vklachkov/grid-compass-fdd-2102/pal (300230-00)/16L8.jpg

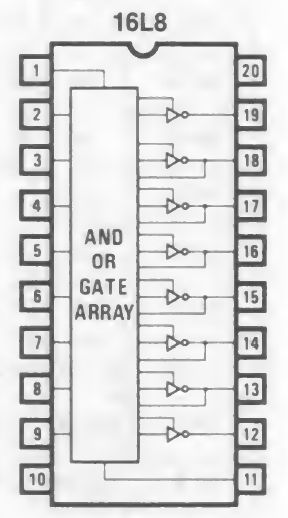
pal (300230-00)/16L8.jpg
