vklachkov/grid-compass-fdd-2102/pal (300230-00)/Logisim_Evolution/PAL16L8.png

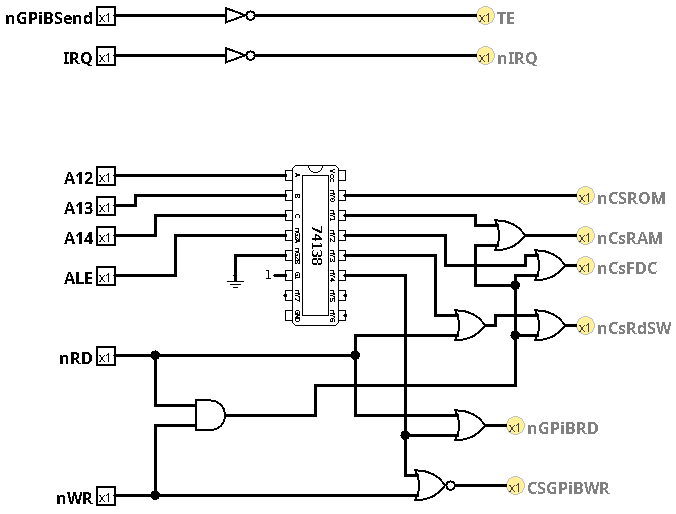
pal (300230-00)/Logisim_Evolution/PAL16L8.png
