vklachkov/grid-compass-fdd-2102/schematic/AC_Wiring.kicad_sch

## KiCad design schematic/AC_Wiring.kicad_sch (2025-12-12)

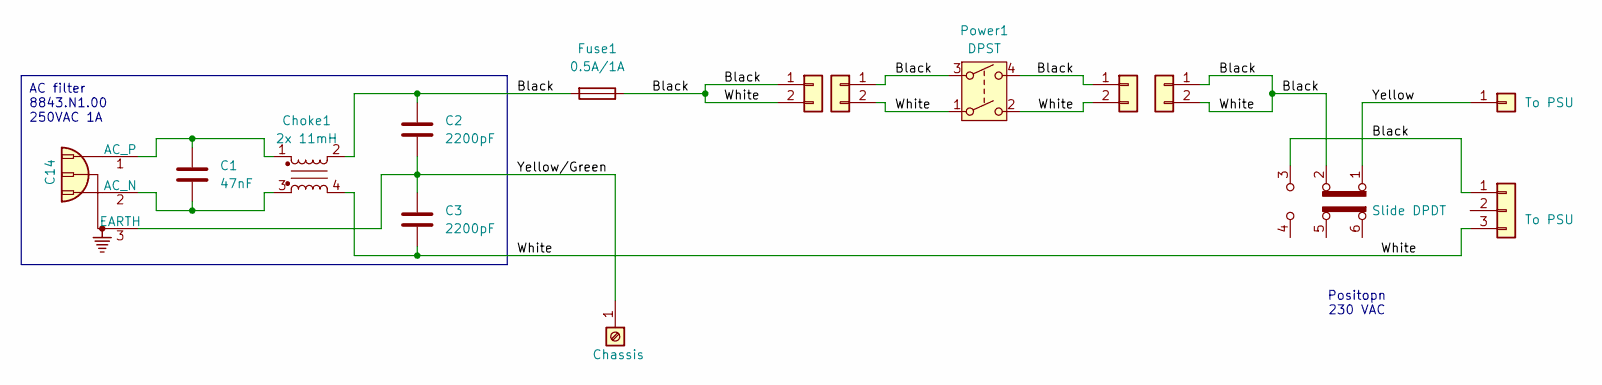
[picture p20: schematic AC_Wiring.kicad_sch]

Parts:
110/1: Slide DPDT
C1: 47nF
C2, C3: 2200pF
Choke1: 2x 11mH; Choke_Schaffner_RN102-04-14.0x14.0mm
Fuse1: 0.5A/1A
J1: C14
J2: Chassis
J3, J4, J5, J6: Conn_01x02
J7: To PSU
J8: To PSU; JST_VH_B3P-VH-B_1x03_P3.96mm_Vertical
Power1: DPST

Connections:
Black: 110/1.2 (B), 110/1.3 (C), C2.1, C3.2, Choke1.2, Choke1.4, Fuse1.1, Fuse1.2, J3.1, J3.2, J4.1, J4.2, J5.1, J5.2, J6.1, J6.2, J8.1, J8.3, Power1.1, Power1.2, Power1.3, Power1.4
unnamed: C1.1, Choke1.1, J1.1 (AC_P)
unnamed: C1.2, Choke1.3, J1.2 (AC_N)
Yellow: 110/1.1 (A), J7.1
Yellow/Green: C2.2, C3.1, J1.3 (EARTH), J2.1

Notes on the sheet:
AC filter 8843.N1.00 250VAC 1A
Positopn 230 VAC
