vklachkov/grid-compass-fdd-2102/schematic/Floppy_Controller_Board.kicad_sch

## KiCad design schematic/Floppy_Controller_Board.kicad_sch (2025-12-12)

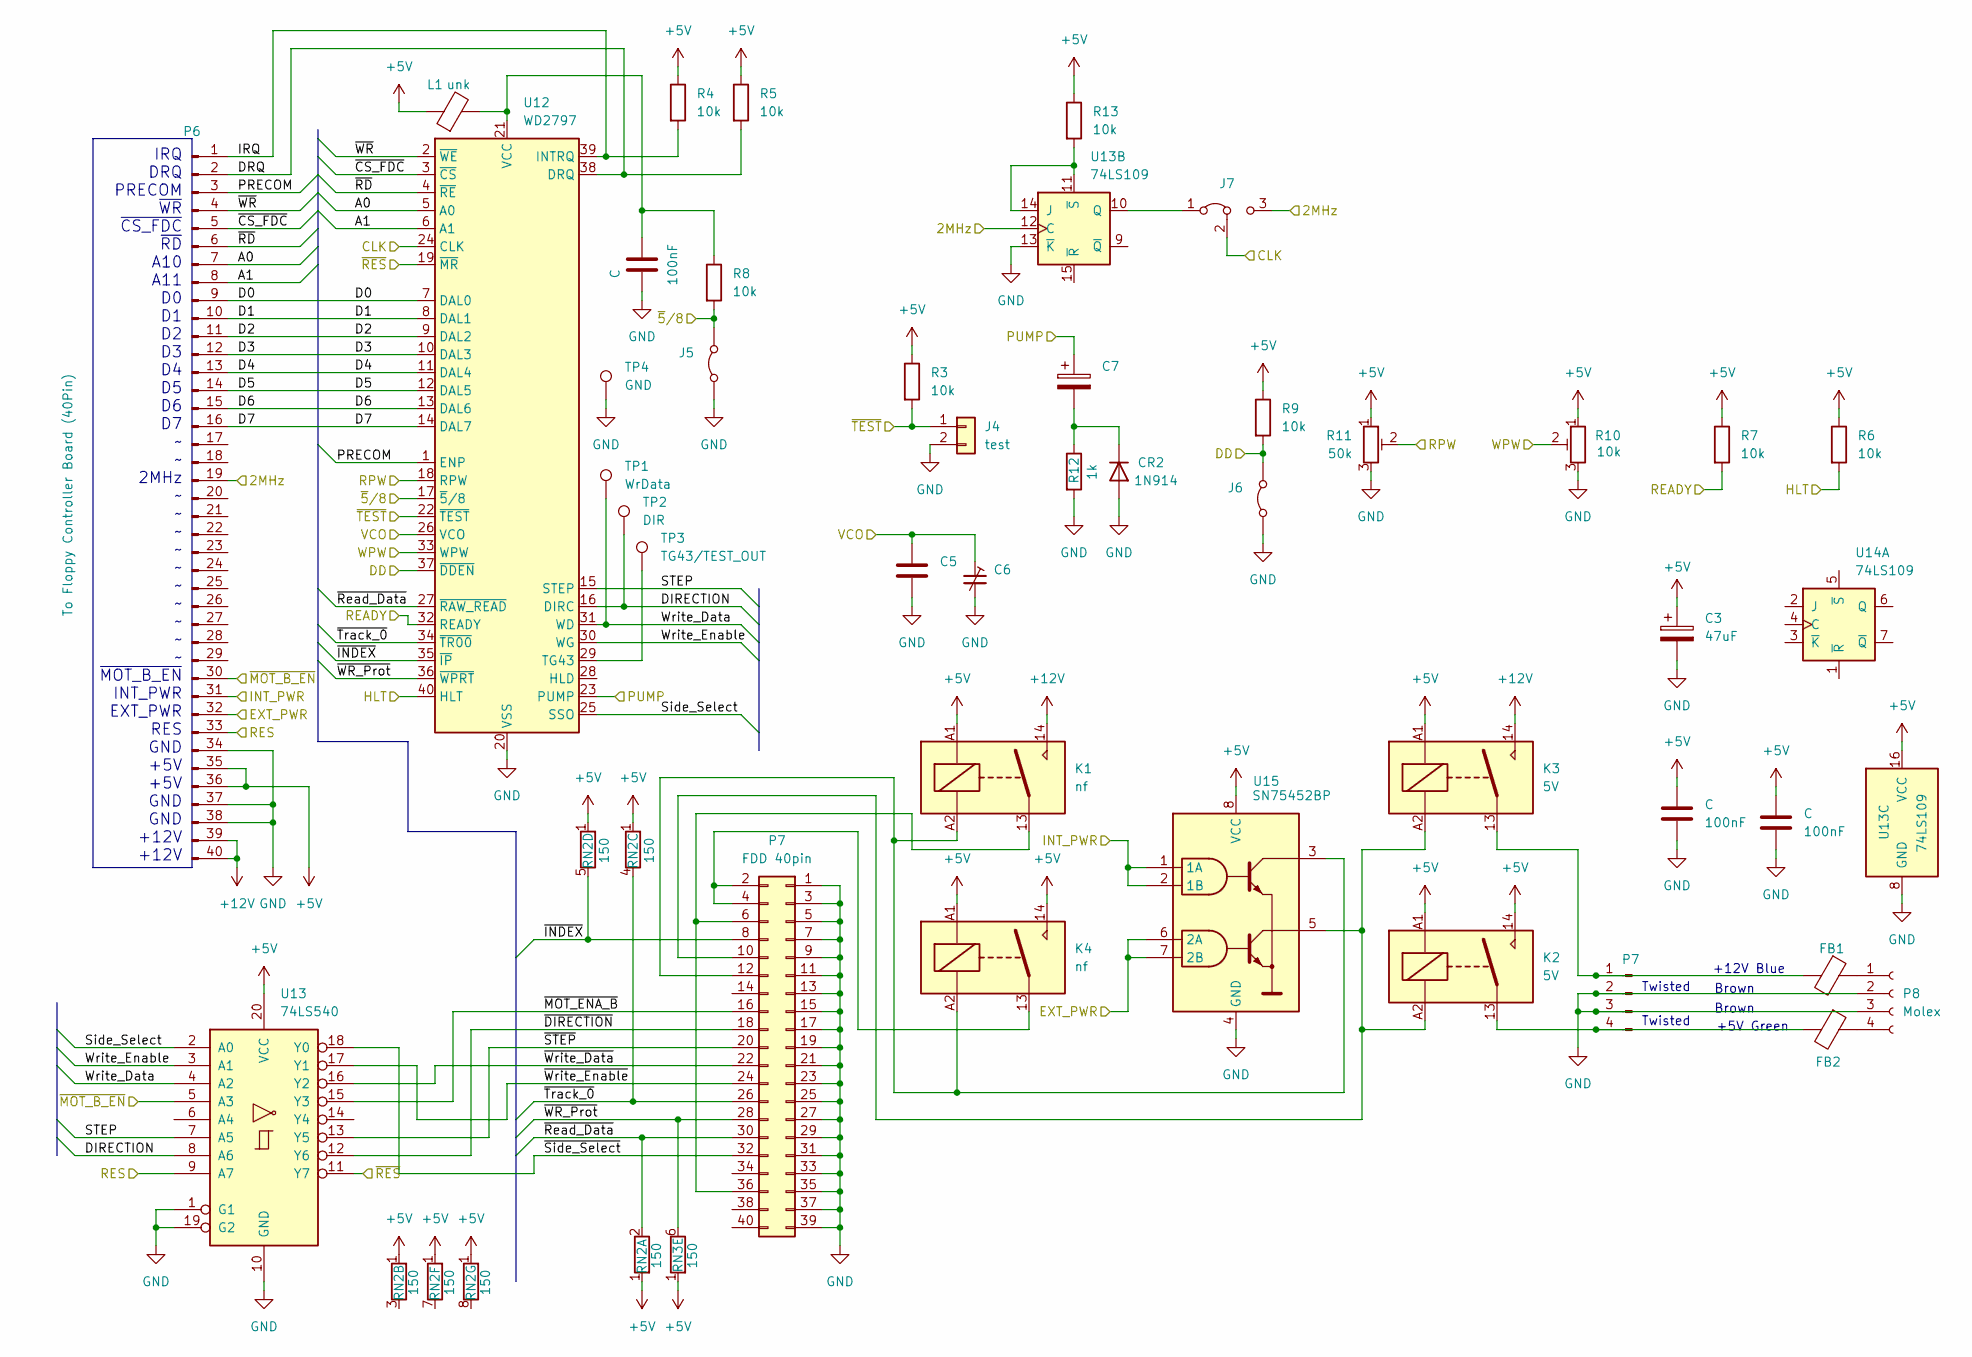
[picture p22: schematic Floppy_Controller_Board.kicad_sch]

Parts:
C: 100nF; C_Disc_D4.3mm_W1.9mm_P5.00mm
C3: 47uF; CP_Axial_L21.0mm_D8.0mm_P28.00mm_Horizontal; Voltage 10V
C5: CP_Axial_L10.0mm_D4.5mm_P15.00mm_Horizontal
C6: C_Disc_D6.0mm_W2.5mm_P5.00mm
C7: CP_Radial_Tantal_D4.5mm_P2.50mm
CR2: 1N914; D_DO-35_SOD27_P10.16mm_Horizontal
FB1, FB2: L_0603_1608Metric
J4: test
J5, J6: (no value)
J7: Jumper_3_Bridged12
K1, K4: nf; Relay_SPST-NO_Fujitsu_FTR-LYAA005x_FormA_Vertical
K2, K3: 5V; Relay_SPST-NO_Fujitsu_FTR-LYAA005x_FormA_Vertical
L1: unk
P6: To Floppy Controller Board (40Pin)
P7: FDD 40pin
P8: Molex; TE_MATE-N-LOK_350211-1_1x04_P5.08mm_Vertical
R3, R4, R5, R6, R7, R8, R9, R13: 10k; R_Axial_DIN0309_L9.0mm_D3.2mm_P12.70mm_Horizontal
R10: 10k; Potentiometer_ACP_CA6-H2,5_Horizontal
R11: 50k; Potentiometer_ACP_CA6-H2,5_Horizontal
R12: 1k; R_Axial_DIN0309_L9.0mm_D3.2mm_P12.70mm_Horizontal
RN2, RN3: 150; R_Array_SIP8
TP1: WrData
TP2: DIR
TP3: TG43/TEST_OUT
TP4: GND
U12: WD2797; DIP-40_W15.24mm
U13, U14: 74LS109; DIP-16_W7.62mm
U15: SN75452BP; DIP-8_W7.62mm

Connections:
2MHz: J7.3 (B), P6.19, U13.12 (Y6)
+5V: C.1, C3.1, K1.A1, K2.14, K2.A1, K3.A1, K4.14, K4.A1, L1.1, P6.35, P6.36, R3.1, R4.1, R5.1, R6.1, R7.1, R9.1, R10.1, R11.1, R13.1, RN2.1 (R1), RN3.1 (R1), U13.16 (Y2), U13.20 (VCC), U15.8 (VCC)
+12V: K1.14, K3.14, P6.39, P6.40
A0: P6.7, U12.5 (A0)
A1: P6.8, U12.6 (A1)
CLK: J7.2 (C), U12.24 (CLK)
D0: P6.9, U12.7 (DAL0)
D1: P6.10, U12.8 (DAL1)
D2: P6.11, U12.9 (DAL2)
D3: P6.12, U12.10 (DAL3)
D4: P6.13, U12.11 (DAL4)
D5: P6.14, U12.12 (DAL5)
D6: P6.15, U12.13 (DAL6)
D7: P6.16, U12.14 (DAL7)
DD: J6.2 (B), R9.2, U12.37 (~DDEN)
DIRECTION: TP2.1, U12.16 (DIRC), U13.8 (A6)
DRQ: P6.2, R5.2, U12.38 (DRQ)
EXT_PWR: P6.32, U15.6 (2A), U15.7 (2B)
GND: C.2, C3.2, C5.2, C6.2, CR2.2 (A), J4.2, J5.1 (A), J6.1 (A), P6.34, P6.37, P6.38, P7.1, P7.2, P7.3, P7.5, P7.7, P7.9, P7.11, P7.13, P7.15, P7.17, P7.19, P7.21, P7.23, P7.25, P7.27, P7.29, P7.31, P7.33, P7.35, P7.37, P7.39, P8.2, P8.3, R10.3, R11.3, R12.2, TP4.1, U12.20 (VSS), U13.1 (G1), U13.8 (A6), U13.10 (GND), U13.13 (Y5), U13.19 (G2), U15.4 (GND)
HLT: R6.2, U12.40 (HLT)
INT_PWR: P6.31, U15.1 (1A), U15.2 (1B)
IRQ: P6.1, R4.2, U12.39 (INTRQ)
unnamed: C7.2, CR2.1 (K), R12.1
unnamed: C.1, L1.2, R8.1, U12.21 (VCC)
unnamed: FB1.1, P8.1
unnamed: FB1.2, K3.13, P7.1
unnamed: FB2.1, P8.4
unnamed: FB2.2, K2.13, P7.4
unnamed: J7.1 (A), U13.10 (GND)
unnamed: K1.13, P7.6, P7.36
unnamed: K1.A2, K4.A2, P7.12, U15.3
unnamed: K2.A2, K3.A2, P7.10, U15.5
unnamed: K4.13, P7.2, P7.4
unnamed: R13.2, U13.11 (Y7), U13.14 (Y4)
unnamed: TP3.1, U12.29 (TG43)
PRECOM: P6.3, U12.1 (ENP)
PUMP: C7.1, U12.23 (PUMP)
READY: R7.2, U12.32 (READY)
RES: P6.33, U13.9 (A7)
RPW: R11.2, U12.18 (RPW)
STEP: U12.15 (STEP), U13.7 (A5)
Side_Select: U12.25 (SSO), U13.2 (A0)
VCO: C5.1, C6.1, U12.26 (VCO)
WPW: R10.2, U12.33 (WPW)
Write_Data: TP1.1, U12.31 (WD), U13.4 (A2)
Write_Enable: U12.30 (WG), U13.3 (A1)
~5/8: J5.2 (B), R8.2, U12.17 (~5/8)
~CS_FDC: P6.5, U12.3 (~CS)
~DIRECTION: P7.18, U13.12 (Y6)
~INDEX: P7.8, RN2.5 (R4.2), U12.35 (~IP)
~MOT_B_EN: P6.30, U13.5 (A3)
~MOT_ENA_B: P7.16, U13.15 (Y3)
~RD: P6.6, U12.4 (~RE)
~RES: U12.19 (~MR), U13.11 (Y7)
~Read_Data: P7.30, RN2.2 (R1.2), U12.27 (~RAW_READ)
~STEP: P7.20, U13.13 (Y5)
~Side_Select: P7.32, U13.18 (Y0)
~TEST: J4.1, R3.2, U12.22 (~TEST)
~Track_0: P7.26, RN2.4 (R3.2), U12.34 (~TR00)
~WR_Prot: P7.28, RN3.6 (R5.2), U12.36 (~WPRT)
~WR: P6.4, U12.2 (~WE)
~Write_Data: P7.22, U13.16 (Y2)
~Write_Enable: P7.24, U13.17 (Y1)

Notes on the sheet:
IRQ DRQ PRECOM ~{WR} ~{CS_FDC} ~{RD} A10 A11 D0 D1 D2 D3 D4 D5 D6 D7 ~ ~ 2MHz ~ ~ ~ ~ ~ ~ ~ ~ ~ ~ ~{MOT_B_EN} INT_PWR EXT_PWR RES GND +5V +5V GND GND +12V +12V
Brown
+12V Blue
+5V Green
Twisted
