vklachkov/grid-compass-fdd-2102/schematic/GPiB_connector.kicad_sch

## KiCad design schematic/GPiB_connector.kicad_sch (2025-12-12)

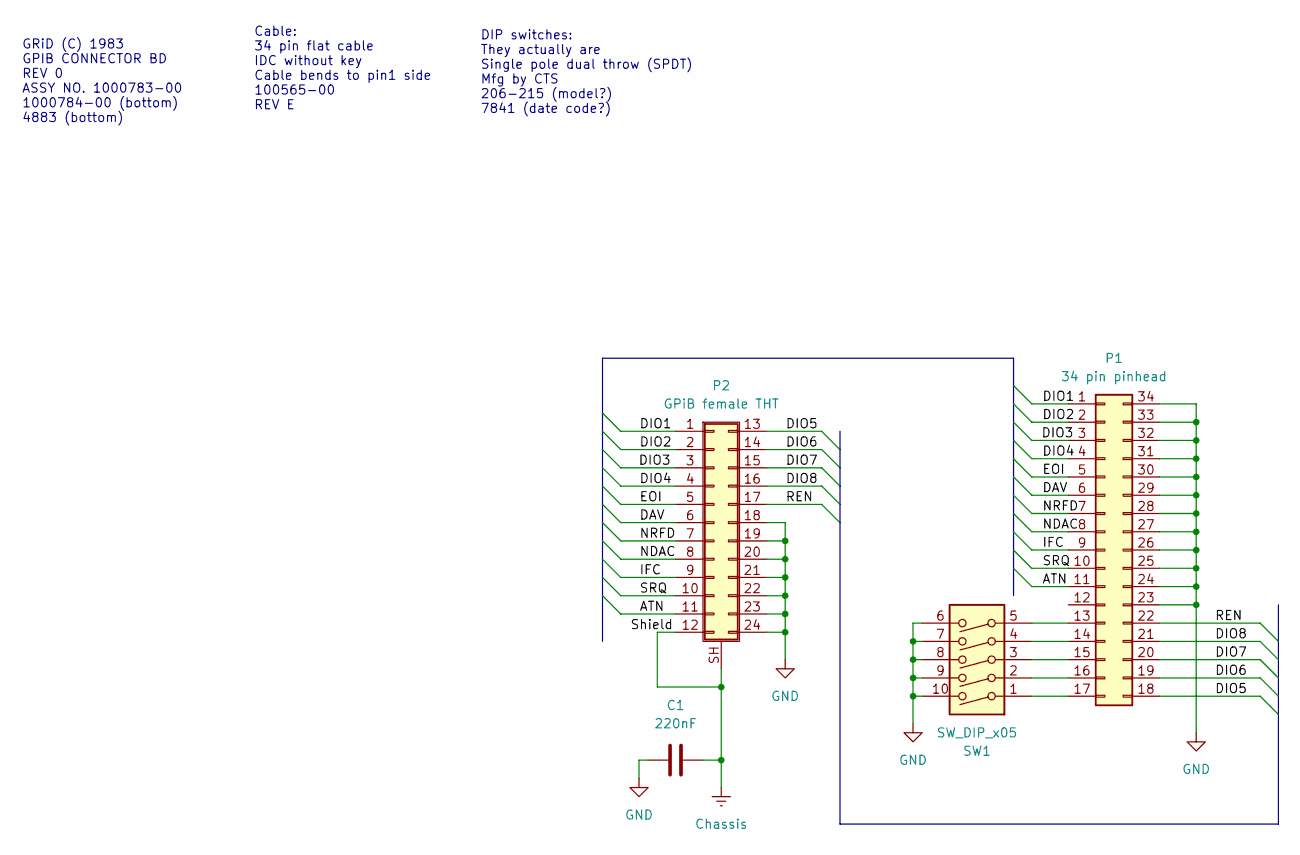
[picture p24: schematic GPiB_connector.kicad_sch]

Parts:
C1: 220nF; C_Rect_L10.0mm_W2.5mm_P7.50mm_MKS4; Voltage 100V
P1: 34 pin pinhead
P2: GPiB female THT
SW1: SW_DIP_x05

Connections:
ATN: P1.11, P2.11
Chassis: C1.2, P2.12, P2.SH (Shield)
DAV: P1.6, P2.6
DIO1: P1.1, P2.1
DIO2: P1.2, P2.2
DIO3: P1.3, P2.3
DIO4: P1.4, P2.4
DIO5: P1.18, P2.13
DIO6: P1.19, P2.14
DIO7: P1.20, P2.15
DIO8: P1.21, P2.16
EOI: P1.5, P2.5
GND: C1.1, P1.23, P1.24, P1.25, P1.26, P1.27, P1.28, P1.29, P1.30, P1.31, P1.32, P1.33, P1.34, P2.18, P2.19, P2.20, P2.21, P2.22, P2.23, P2.24, SW1.6, SW1.7, SW1.8, SW1.9, SW1.10
IFC: P1.9, P2.9
NDAC: P1.8, P2.8
NRFD: P1.7, P2.7
unnamed: P1.13, SW1.5
unnamed: P1.14, SW1.4
unnamed: P1.15, SW1.3
unnamed: P1.16, SW1.2
unnamed: P1.17, SW1.1
REN: P1.22, P2.17
SRQ: P1.10, P2.10

Notes on the sheet:
Cable: 34 pin flat cable IDC without key Cable bends to pin1 side 100565-00 REV E
DIP switches: They actually are Single pole dual throw (SPDT) Mfg by CTS 206-215 (model?) 7841 (date code?)
GRiD (C) 1983 GPIB CONNECTOR BD REV 0 ASSY NO. 1000783-00 1000784-00 (bottom) 4883 (bottom)
