vklachkov/grid-compass-fdd-2102/pal (300230-00)/PAL16L8_dumper/megaprogrammer28.py

#!/usr/bin/env python
# Uses the Arduino firmware given on http://danceswithferrets.org/geekblog/?p=496
#
# -r start end (in decimal) dump address+data+checksum
# -R start end (in decimal) dump only data
# -b start end (in decimal) dump in binary
# -s file.bin (programming)
# -v file.bin (verify content)
# -S file.bin ('smart' programming)
#
# Normally takes 196 seconds to program a 28C64, and 32 seconds to read.
# --
# Chris Baird,, <cjb@brushtail.apana.org.au> threw
# this together during an all-nighter on 2017-Oct-19.
# This version: 2017-Oct-25.

from __future__ import print_function

import sys
import serial
import time
import os

RECSIZE = 16

# ser = serial.Serial('/dev/ttyACM0', 115200, timeout=0.1)
ser = serial.Serial('/dev/ttyUSB0', 115200, timeout=0.1)
# ser = open('serial_out.dbg', 'wb')  # DBG

sys.argv.pop(0)
dumpstart = -1
dumpend = -1
s = sys.argv[0]
time.sleep(1)                   # weirdness it started needing -cjb
ser.flush()
time.sleep(1)

PY3 = sys.version_info[0] >= 3


def ord_compat(c):
    if PY3:
        return c
    else:
        return ord(c)

def bytes_compat(s):
    if PY3:
        return s.encode()
    else:
        return s


def calcwriteline(a, l):
    ck = 0
    s = "W" + ("%05x" % a) + ":"
    for c in l:
        s = s + ("%02x" % ord_compat(c))
        ck = ck ^ ord_compat(c)
    s = s + "ffffffffffffffffffffffffffffffff"
    #print(s)
    s = s[:39]
    if (len(l) & 1):
        ck = ck ^ 255
    ck = ck & 255
    s = s + "," + ("%02x" % ck)
    return s.upper()


def waitokay():
    bad = 0
    while True:
        s = ser.readline()
        # s = sys.stdin.readline()  # DBG

        # print(s)  # DBG
        # time.sleep(.1)  # DBG

        # if s == "OK\r\n":
        if s.startswith(b"OK"):
            break
        else:
            bad = bad + 1
        if bad > 50:
            sys.exit("F*ck!")


if s == "-r":
    dumpstart = int(sys.argv[1])
    dumpend = int(sys.argv[2])
    print("\n\n")
    
    if dumpstart > -1:
        while (dumpstart <= dumpend):
            addr = "%05x" % dumpstart
            s = "R" + addr + chr(10)
            ser.flush()
            ser.write(bytes_compat(s))
            time.sleep(.1)
            l = ser.readline()
            #print(l.upper(), end='')
            print(l.upper())
            print("\n")
            waitokay()
            dumpstart = dumpstart + RECSIZE


if s == "-R":
    dumpstart = int(sys.argv[1])
    dumpend = int(sys.argv[2])
    if dumpstart > -1:
        while (dumpstart <= dumpend):
            addr = "%05x" % dumpstart
            s = "R" + addr + chr(10)
            ser.flush()
            ser.write(bytes_compat(s))
            time.sleep(.1)
            l = ser.readline()
            o = l.upper()
            content = o[6:-6]
            for i in range(0,64,2):
                by = content[i:i+2]
                print(by, end='')
            print()
            waitokay()
            dumpstart = dumpstart + RECSIZE


if s == "-b":
    dumpstart = int(sys.argv[1])
    dumpend = int(sys.argv[2])
    if dumpstart > -1:
        while (dumpstart <= dumpend):
            addr = "%05x" % dumpstart
            s = "R" + addr + chr(10)
            ser.flush()
            ser.write(bytes_compat(s))
            time.sleep(.1)
            l = ser.readline()
            o = l.upper()
            content = o[6:-6]
            for i in range(0,64,2):
                by = content[i:i+2]
                #print(i/2),
                #print(l),
                #print(by)
                if by.strip():
                #print(i/2),
                #print(by),
                #print( int(by, 16) )
                    sys.stdout.write(chr(int(by, 16))),
            sys.stderr.write(o[0:5])
            sys.stderr.write('\n')
            waitokay()
            dumpstart = dumpstart + RECSIZE


if s == "-s":
    statinfo = os.stat(sys.argv[1])
    fileSize=statinfo.st_size
    f = open(sys.argv[1], 'rb')
    a = 0
    while True:
        l = f.read(RECSIZE)
        if len(l) == 0:
            break
        s = calcwriteline(a, l)
        #print(s)
        sys.stdout.flush()
        #ser.flush()
        print(" %s %0.2f%%" % (s, (float(a)/float(fileSize))*100))
        ser.write(bytes_compat(s + chr(10)))
        waitokay()
        sys.stdout.flush()
        if len(l) != RECSIZE:
            break
        a = a + RECSIZE
    f.close()


if s == "-v":
    f = open(sys.argv[1], 'rb')
    a = 0
    badcount = 0
    while True:
        s = "R" + ("%05x" % a) + chr(10)
        #ser.flush()
        ser.write(bytes_compat(s))
        time.sleep(.1)
        l = ser.readline()
        l = l.upper()
        #print(l)
        waitokay()


        romt = "ROM  %05x:" % a

        
        rom = [None]*RECSIZE
        for p in range(RECSIZE):
            i = 6 + (p*2)
            #print(i)
            if l[i:i+2].strip():
                c = int(l[i:i+2], 16)
                romt = romt + str(" %02x" % c)
                rom[p] = c
        print(romt)
        sys.stdout.flush()

        r = f.read(RECSIZE)
        if len(r) == 0:
            break
        okay = 1
        filet = "FILE %05x:" % a
        for i in range(len(r)):
            filet = filet + " %02x" % ord_compat(r[i])
            if rom[i] != ord_compat(r[i]):
                okay = 0
                badcount = badcount + 1

        if okay == 0:
            print()
            print(filet)
            print("MISMATCH!!")
            print()
            sys.stdout.flush()

        if len(r) != RECSIZE:
            break
        else:
            a = a + RECSIZE

    print()
    print(badcount, "errors!")
    sys.stdout.flush()
    f.close()


if s == "-S":
    f = open(sys.argv[1], 'rb')
    a = 0
    while True:
        s = "R" + ("%05x" % a) + chr(10)
        ser.flush()
        ser.write(bytes_compat(s))
        l = ser.readline()
        l = l.upper()
        waitokay()

        romt = "ROM  %05x:" % a
        rom = [None]*RECSIZE
        for p in range(RECSIZE):
            i = 6 + (p*2)
            c = int(l[i:i+2], 16)
            romt = romt + str(" %02x" % c)
            rom[p] = c

        r = f.read(RECSIZE)
        if len(r) == 0:
            break
        print(romt, end='')
        sys.stdout.flush()
        okay = 1
        filet = "FILE %05x:" % a
        for i in range(len(r)):
            if rom[i] != ord_compat(r[i]):
                okay = 0
                filet = filet + " %02x" % ord_compat(r[i])
            else:
                filet = filet + "   "

        if okay == 0:
            s = calcwriteline(a, r)
            print()
            print(filet, "UPDATING")
            sys.stdout.flush()
            ser.write(bytes_compat(s+chr(10)))
            waitokay()
        else:
            print(" OKAY")
        sys.stdout.flush()

        if len(r) != RECSIZE:
            break
        else:
            a = a + RECSIZE

    f.close()

###
